ratnick/CarDashboard/3D print/Phone_mount_for_Lotus_Elise_Exige/images/3f115b13c07ff41f2abeaf240fafdb68_preview_featured.jpg

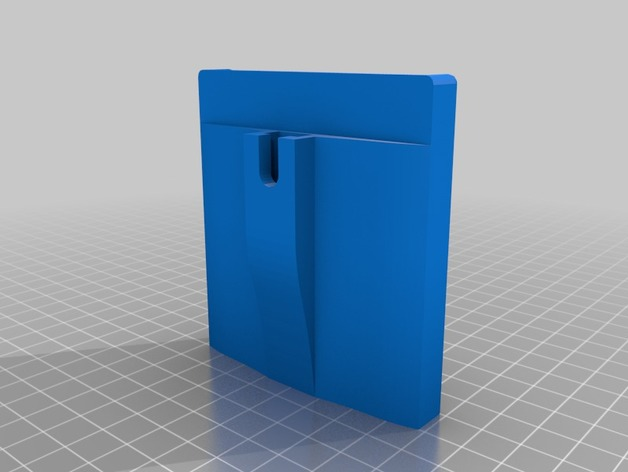
3D print/Phone_mount_for_Lotus_Elise_Exige/images/3f115b13c07ff41f2abeaf240fafdb68_preview_featured.jpg
