ratnick/CarDashboard/3D print/Phone_mount_for_Lotus_Elise_Exige/images/c0602b64a66d1e5e7128305c19cd4e9d_preview_featured.jpg

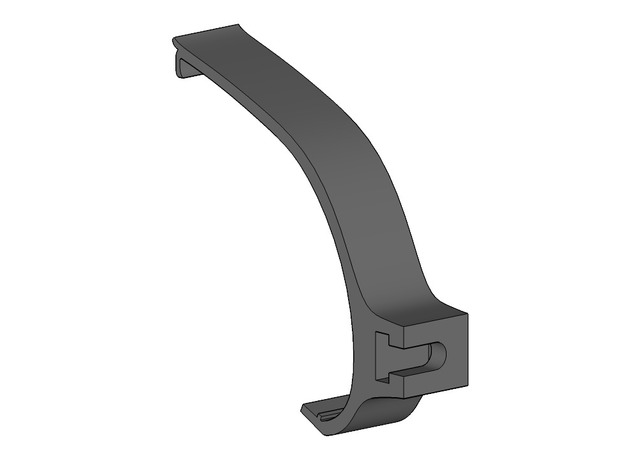
3D print/Phone_mount_for_Lotus_Elise_Exige/images/c0602b64a66d1e5e7128305c19cd4e9d_preview_featured.jpg
