ratnick/CarDashboard/3D print/Phone_mount_for_Lotus_Elise_Exige/images/d24fa7f10c37b9a051e7b17cd339253a_preview_featured.JPG

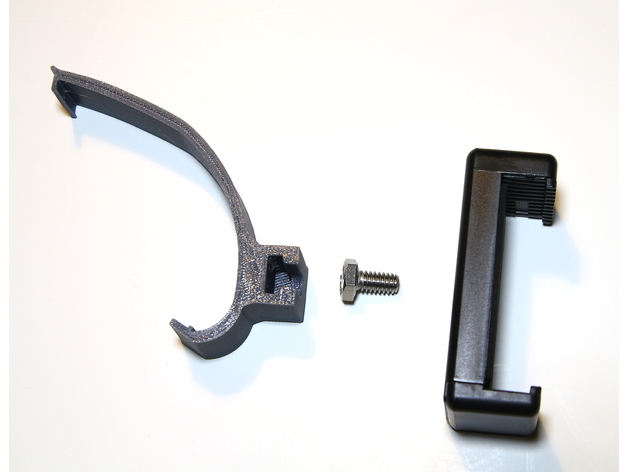
3D print/Phone_mount_for_Lotus_Elise_Exige/images/d24fa7f10c37b9a051e7b17cd339253a_preview_featured.JPG
