ratnick/CarDashboard/Arduino/OTAtest/OTAtest.ino

/*
 Name:		OTAtest.ino
 Created:	12/6/2020 5:20:37 PM
 Author:	Nikolaj (lokal)
*/

#include <ESP8266WiFi.h>
#include <ESP8266mDNS.h>
#include <WiFiUdp.h>
#include <ArduinoOTA.h>

#ifndef STASSID
#define STASSID "nohrTDC"
#define STAPSK  "RASMUSSEN"
#endif

const char* ssid = STASSID;
const char* password = STAPSK;

//variabls for blinking an LED with Millis
const int led = 2; // ESP32 Pin to which onboard LED is connected
unsigned long previousMillis = 0;  // will store last time LED was updated
const long interval = 3000;  // interval at which to blink (milliseconds)
bool ledState = LOW;  // ledState used to set the LED


void SetupOTA() {

    // Port defaults to 8266
    // ArduinoOTA.setPort(8266);

    // Hostname defaults to esp8266-[ChipID]
    // ArduinoOTA.setHostname("myesp8266");

    // No authentication by default
    // ArduinoOTA.setPassword("admin");

    // Password can be set with it's md5 value as well
    // MD5(admin) = 21232f297a57a5a743894a0e4a801fc3
    // ArduinoOTA.setPasswordHash("21232f297a57a5a743894a0e4a801fc3");

    ArduinoOTA.onStart([]() {
        String type;
        if (ArduinoOTA.getCommand() == U_FLASH) {
            type = "sketch";
        }
        else { // U_FS
            type = "filesystem";
        }

        // NOTE: if updating FS this would be the place to unmount FS using FS.end()
        Serial.println("Start updating " + type);
    });
    ArduinoOTA.onEnd([]() {
        Serial.println("\nEnd");
    });
    ArduinoOTA.onProgress([](unsigned int progress, unsigned int total) {
        Serial.printf("Progress: %u%%\r", (progress / (total / 100)));
    });
    ArduinoOTA.onError([](ota_error_t error) {
        Serial.printf("Error[%u]: ", error);
        if (error == OTA_AUTH_ERROR) {
            Serial.println("Auth Failed");
        }
        else if (error == OTA_BEGIN_ERROR) {
            Serial.println("Begin Failed");
        }
        else if (error == OTA_CONNECT_ERROR) {
            Serial.println("Connect Failed");
        }
        else if (error == OTA_RECEIVE_ERROR) {
            Serial.println("Receive Failed");
        }
        else if (error == OTA_END_ERROR) {
            Serial.println("End Failed");
        }
    });
    ArduinoOTA.begin();
    Serial.println("Ready");
    Serial.print("IP address: ");
    Serial.println(WiFi.localIP());
}

void setup() {
    Serial.begin(115200);
    Serial.println("Booting");
    WiFi.mode(WIFI_STA);
    WiFi.begin(ssid, password);
    while (WiFi.waitForConnectResult() != WL_CONNECTED) {
        Serial.println("Connection Failed! Rebooting...");
        delay(5000);
        ESP.restart();
    }

    SetupOTA();
    pinMode(led, OUTPUT);
}

void loop() {
    ArduinoOTA.handle();

    //loop to blink without delay
    unsigned long currentMillis = millis();
    if (currentMillis - previousMillis >= interval) {
        // save the last time you blinked the LED
        previousMillis = currentMillis;
        // if the LED is off turn it on and vice-versa:
        ledState = not(ledState);
        // set the LED with the ledState of the variable:
        digitalWrite(LED_BUILTIN, ledState);
        Serial.print("y");
    }
}
